developer-journey/stewart-platform/tutorial/servo-arm-control-rod-assembly.png

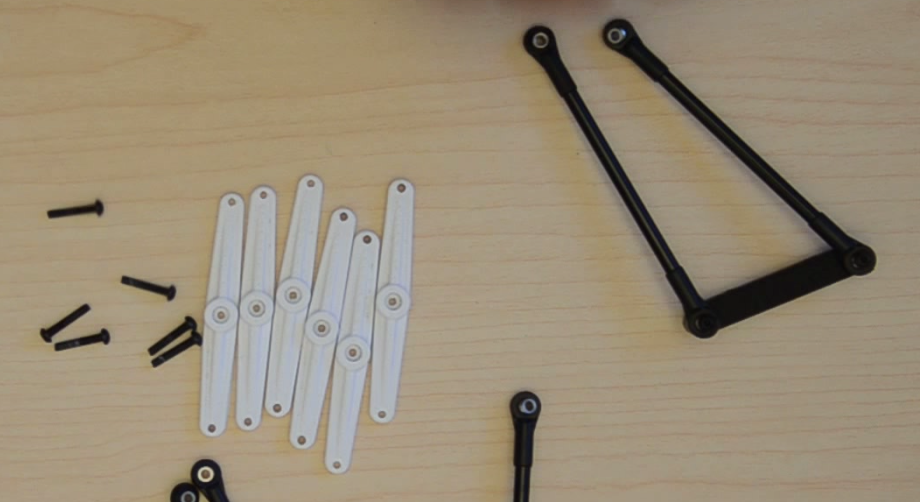
tutorial/servo-arm-control-rod-assembly.png
